mynemjef/Ghost-Bat-UAV/Code/relay.ino

#define relay1   2
#define relay2   4

void setup() {
  pinMode(relay1, OUTPUT);
  pinMode(relay2, OUTPUT);
}

void loop() {
  digitalWrite(relay1, LOW);
  digitalWrite(relay2, LOW);
  delay(1000); 
  digitalWrite(relay1, HIGH);
  digitalWrite(relay2, HIGH);
  delay(1000);
}
